ltebs-polimi/AY2122_II_Project-1/Project_LTEBS/Saturimetro.cydsn/I2C_Interface.c

/*
* This file includes all the required source code to interface
* the I2C peripheral.
*/


#include "I2C_Interface.h" 
#include "I2C_Master.h"

    uint8_t I2C_Peripheral_Start(void) 
    {
        // Start I2C peripheral
        I2C_Master_Start();  
        
        // Return no error since start function does not return any error
        return I2C_NO_ERROR;
    }
    
    
    uint8_t I2C_Peripheral_Stop(void)
    {
        // Stop I2C peripheral
        I2C_Master_Stop();
        // Return no error since stop function does not return any error
        return I2C_NO_ERROR;
    }
    
    uint8_t I2C_Peripheral_SendStop(void)
    {
        I2C_Master_MasterSendStop();
        return I2C_NO_ERROR;
    }
    
    uint8_t I2C_Peripheral_ReadRegister(uint8_t device_address, 
                                            uint8_t register_address,
                                            uint8_t* data)
    {
        // Send start condition
        uint8_t error = I2C_Master_MasterSendStart(device_address,I2C_Master_WRITE_XFER_MODE);
        if (error == I2C_Master_MSTR_NO_ERROR)
        {
            // Write address of register to be read
            error = I2C_Master_MasterWriteByte(register_address);
            if (error == I2C_Master_MSTR_NO_ERROR)
            {
                // Send restart condition
                error = I2C_Master_MasterSendRestart(device_address, I2C_Master_READ_XFER_MODE);
                if (error == I2C_Master_MSTR_NO_ERROR)
                {
                    // Read data without acknowledgement
                    *data = I2C_Master_MasterReadByte(I2C_Master_ACK_DATA);
                    // Send stop condition and return no error
                    I2C_Master_MasterSendStop();
                    return I2C_NO_ERROR;
                }
            }
        }
        // Send stop condition if something went wrong
        I2C_Master_MasterSendStop();
        // Return error code
        return I2C_DEV_NOT_FOUND;
    }
    
    uint8_t I2C_Peripheral_ReadRegisterMulti(uint8_t device_address,
                                                uint8_t register_address,
                                                uint16_t register_count,
                                                uint8_t* data)
    {
        // Send start condition
        uint8_t error = I2C_Master_MasterSendStart(device_address,I2C_Master_WRITE_XFER_MODE);
        if (error == I2C_Master_MSTR_NO_ERROR)
        {
            // Write address of register to be read with the MSB equal to 1
            // register_address |= 0x80;
            error = I2C_Master_MasterWriteByte(register_address);
            if (error == I2C_Master_MSTR_NO_ERROR)
            {
                // Send restart condition
                error = I2C_Master_MasterSendRestart(device_address, I2C_Master_READ_XFER_MODE);
                if (error == I2C_Master_MSTR_NO_ERROR)
                {
                    // Continue reading until we have register to read
                    uint16_t counter = register_count;
                    while(counter>1)
                    {
                        data[register_count-counter] =
                            I2C_Master_MasterReadByte(I2C_Master_ACK_DATA);
                        counter--;
                    }
                    // Read last data without acknowledgement
                    data[register_count-1]
                        = I2C_Master_MasterReadByte(I2C_Master_NAK_DATA);
                    // Send stop condition and return no error
                    I2C_Master_MasterSendStop();
                    return I2C_NO_ERROR;
                }
            }
        }
        // Send stop condition if something went wrong
        I2C_Master_MasterSendStop();
        // Return error code
        return I2C_DEV_NOT_FOUND;
    }
    
    uint8_t I2C_Peripheral_ReadRegisterMultiNoAddress(uint8_t device_address,
                                                      uint16_t register_count, 
                                                      uint8_t* data)
    {
        // Send restart condition
        uint8_t error = I2C_Master_MasterSendStart(device_address, I2C_Master_READ_XFER_MODE);
        if (error == I2C_Master_MSTR_NO_ERROR)
        {
            // Continue reading until we have register to read
            uint16_t counter = register_count;
            while(counter>1)
            {
                data[register_count-counter] =
                    I2C_Master_MasterReadByte(I2C_Master_ACK_DATA);
                counter--;
            }
            // Read last data without acknowledgement
            data[register_count-1] = I2C_Master_MasterReadByte(I2C_Master_NAK_DATA);
            // Send stop condition and return no error
            I2C_Master_MasterSendStop();
            return I2C_NO_ERROR;
        }
        // Send stop condition if something went wrong
        I2C_Master_MasterSendStop();
        // Return error code
        return I2C_DEV_NOT_FOUND;
    }
    
    uint8_t I2C_Peripheral_StartReadNoAddress(uint8_t device_address)
    {
        // Send restart condition
        uint8_t error = I2C_Master_MasterSendStart(device_address, I2C_Master_READ_XFER_MODE);
        if (error == I2C_Master_MSTR_NO_ERROR)
        {
            return I2C_NO_ERROR;
        }
        // Return error code
        return I2C_DEV_NOT_FOUND;
    }
    
    uint8_t I2C_Peripheral_ReadBytes(uint8_t* data, uint8_t len)
    {
        // Continue reading until we have register to read
        uint16_t counter = len;
        while(counter>1)
        {
            data[len-counter] = I2C_Master_MasterReadByte(I2C_Master_ACK_DATA);
            counter--;
        }
        
        return I2C_NO_ERROR;
    }
    
    uint8_t I2C_Peripheral_WriteRegister(uint8_t device_address,
                                            uint8_t register_address,
                                            uint8_t data)
    {
        // Send start condition
        uint8_t error = I2C_Master_MasterSendStart(device_address, I2C_Master_WRITE_XFER_MODE);
        if (error == I2C_Master_MSTR_NO_ERROR)
        {
            // Write register address
            error = I2C_Master_MasterWriteByte(register_address);
            if (error == I2C_Master_MSTR_NO_ERROR)
            {
                // Write byte of interest
                error = I2C_Master_MasterWriteByte(data);
                if (error == I2C_Master_MSTR_NO_ERROR)
                {
                    // Send stop condition
                    I2C_Master_MasterSendStop();
                    // Return with no error
                    return I2C_NO_ERROR;
                }
            }
        }
        // Send stop condition in case something didn't work out correctly
        I2C_Master_MasterSendStop();
        // Return error code
        return I2C_DEV_NOT_FOUND;
    }
    
    uint8_t I2C_Peripheral_WriteRegisterNoData(uint8_t device_address,
                                            uint8_t register_address)
    {
        // Send start condition
        uint8_t error = I2C_Master_MasterSendStart(device_address, I2C_Master_WRITE_XFER_MODE);
        if (error == I2C_Master_MSTR_NO_ERROR)
        {
            // Write register address
            error = I2C_Master_MasterWriteByte(register_address);
            if (error == I2C_Master_MSTR_NO_ERROR)
            {
                // Send stop condition
                I2C_Master_MasterSendStop();
                // Return with no error
                return I2C_NO_ERROR;
                
            }
        }
        // Send stop condition in case something didn't work out correctly
        I2C_Master_MasterSendStop();
        // Return error code
        return I2C_DEV_NOT_FOUND;
    }
    
    uint8_t I2C_Peripheral_WriteRegisterMulti(uint8_t device_address,
                                            uint8_t register_address,
                                            uint8_t register_count,
                                            uint8_t* data)
    {
        // Send start condition
        uint8_t error = I2C_Master_MasterSendStart(device_address, I2C_Master_WRITE_XFER_MODE);
        if (error == I2C_Master_MSTR_NO_ERROR)
        {
            // Write register address
            error = I2C_Master_MasterWriteByte(register_address);
            if (error == I2C_Master_MSTR_NO_ERROR)
            {
                // Continue writing until we have data to write
                uint8_t counter = register_count;
                while(counter > 0)
                {
                    error = I2C_Master_MasterWriteByte(data[register_count-counter]);
                    if (error != I2C_Master_MSTR_NO_ERROR)
                    {
                        // Send stop condition
                        I2C_Master_MasterSendStop();
                        // Return error code
                        return I2C_ERROR;
                    }
                    counter--;
                }
                // Send stop condition and return no error
                I2C_Master_MasterSendStop();
                return I2C_NO_ERROR;
            }
        }
        // Send stop condition in case something didn't work out correctly
        I2C_Master_MasterSendStop();
        // Return error code
        return I2C_DEV_NOT_FOUND;
    }
    
    
    uint8_t I2C_Peripheral_IsDeviceConnected(uint8_t device_address)
    {
        // Send a start condition followed by a stop condition
        uint8_t error = I2C_Master_MasterSendStart(device_address, I2C_Master_WRITE_XFER_MODE);
        I2C_Master_MasterSendStop();
        // If no error generated during stop, device is connected
        if (error == I2C_Master_MSTR_NO_ERROR)
        {
            return I2C_NO_ERROR;
        }
        else
        {
            return I2C_DEV_NOT_FOUND;
        }
        
    }

/* [] END OF FILE */
