ltebs-polimi/AY2122_II_Project-1/Project_LTEBS/Saturimetro.cydsn/algorithm.h

/* ========================================
 *
 * Copyright YOUR COMPANY, THE YEAR
 * All Rights Reserved
 * UNPUBLISHED, LICENSED SOFTWARE.
 *
 * CONFIDENTIAL AND PROPRIETARY INFORMATION
 * WHICH IS THE PROPERTY OF your company.
 *
 * ========================================
*/
/** \file algorithm.h ******************************************************
*
* Project: MAXREFDES117#
* Filename: algorithm.h
* Description: This module is the heart rate/SpO2 calculation algorithm header file
*
* Revision History:
*\n 1-18-2016 Rev 01.00 SK Initial release.
*\n
*
* --------------------------------------------------------------------
*
* This code follows the following naming conventions:
*
*\n char              ch_pmod_value
*\n char (array)      s_pmod_s_string[16]
*\n float             f_pmod_value
*\n int32_t           n_pmod_value
*\n int32_t (array)   an_pmod_value[16]
*\n int16_t           w_pmod_value
*\n int16_t (array)   aw_pmod_value[16]
*\n uint16_t          uw_pmod_value
*\n uint16_t (array)  auw_pmod_value[16]
*\n uint8_t           uch_pmod_value
*\n uint8_t (array)   auch_pmod_buffer[16]
*\n uint32_t          un_pmod_value
*\n int32_t *         pn_pmod_value
*
* ------------------------------------------------------------------------- */
/*******************************************************************************
* Copyright (C) 2015 Maxim Integrated Products, Inc., All Rights Reserved.
*
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
* Except as contained in this notice, the name of Maxim Integrated
* Products, Inc. shall not be used except as stated in the Maxim Integrated
* Products, Inc. Branding Policy.
*
* The mere transfer of this software does not imply any licenses
* of trade secrets, proprietary technology, copyrights, patents,
* trademarks, maskwork rights, or any other form of intellectual
* property whatsoever. Maxim Integrated Products, Inc. retains all
* ownership rights.
*******************************************************************************
*/
#ifndef ALGORITHM_H_
#define ALGORITHM_H_
#include "project.h"
//#include "mbed.h"

#define true 1
#define false 0
#define FS 50
#define BUFFER_SIZE  (FS*5) 
#define HR_FIFO_SIZE 7
#define MA4_SIZE  4 // DO NOT CHANGE
#define HAMMING_SIZE  5// DO NOT CHANGE
#define min(x,y) ((x) < (y) ? (x) : (y))

extern const uint16_t auw_hamm[31]; //Hamm=  long16(512* hamming(5)');
//uch_spo2_table is computed as  -45.060*ratioAverage* ratioAverage + 30.354 *ratioAverage + 94.845 ;
extern const uint8_t uch_spo2_table[184];



void maxim_heart_rate_and_oxygen_saturation(uint32_t *pun_ir_buffer ,  int32_t n_ir_buffer_length, uint32_t *pun_red_buffer ,   int32_t *pn_spo2, int8_t *pch_spo2_valid ,  int32_t *pn_heart_rate , int8_t  *pch_hr_valid);
void maxim_find_peaks( int32_t *pn_locs, int32_t *pn_npks,  int32_t *pn_x, int32_t n_size, int32_t n_min_height, int32_t n_min_distance, int32_t n_max_num );
void maxim_peaks_above_min_height( int32_t *pn_locs, int32_t *pn_npks,  int32_t *pn_x, int32_t n_size, int32_t n_min_height );
void maxim_remove_close_peaks( int32_t *pn_locs, int32_t *pn_npks,   int32_t  *pn_x, int32_t n_min_distance );
void maxim_sort_ascend( int32_t *pn_x, int32_t n_size );
void maxim_sort_indices_descend(  int32_t  *pn_x, int32_t *pn_indx, int32_t n_size);

#endif /* ALGORITHM_H_ */
/* [] END OF FILE */
