ltebs-polimi/AY2122_II_Project-1/Project_LTEBS/Saturimetro.cydsn/SpO2_HR.h

/* ========================================
 *
 * Copyright YOUR COMPANY, THE YEAR
 * All Rights Reserved
 * UNPUBLISHED, LICENSED SOFTWARE.
 *
 * CONFIDENTIAL AND PROPRIETARY INFORMATION
 * WHICH IS THE PROPERTY OF your company.
 *
 * ========================================
*/

#include "project.h"
#include <stdbool.h>

#define FreqS 50                   //sampling frequency (nel codice Arduino era 25)
#define BUFFER_SIZE (FreqS * 4)     // così da avere una Buffer Size di 200 
#define MA4_SIZE 4                // DONOT CHANGE
#define min(x,y) ((x) < (y) ? (x) : (y)) //Defined in Arduino.h */

//uch_spo2_table is approximated as  -45.060*ratioAverage* ratioAverage + 30.354 *ratioAverage + 94.845 ;
/*const uint8_t uch_spo2_table[100]={100, 99, 98, 97, 96, 95, 94, 93, 92, 91, 90, 89, 88, 87, 86, 85, 84, 83, 82, 
                                    81, 80, 79, 78, 77, 76, 75, 74, 73, 72, 71, 70, 69, 68, 
                                    67, 66, 65, 64, 63, 62, 61, 60, 59, 58, 57, 56, 55, 54, 53, 52, 51, 
                                    50, 49, 48, 47, 46, 45, 44, 43, 42, 41, 40, 39, 38, 37, 36, 35, 34, 33, 32, 
                                    31, 30, 29, 28, 27, 26, 25, 24, 23, 22, 21, 20, 19, 18, 17, 16, 15, 14, 13, 
                                    12, 11, 10, 9, 8, 7, 6, 5, 4, 3, 2, 1 } ;*/
int32_t an_x[BUFFER_SIZE]; //ir
int32_t an_y[BUFFER_SIZE]; //red

void maxim_heart_rate_and_oxygen_saturation(uint32_t *pun_ir_buffer, int32_t n_buffer_length, uint32_t *pun_red_buffer, int32_t *pn_spo2, int8_t *pch_spo2_valid, int32_t *pn_heart_rate, int8_t *pch_hr_valid);

void maxim_find_peaks(int32_t *pn_locs, int32_t *n_npks,  int32_t  *pn_x, int32_t n_size, int32_t n_min_height, int32_t n_min_distance, int32_t n_max_num);
void maxim_peaks_above_min_height(int32_t *pn_locs, int32_t *n_npks,  int32_t  *pn_x, int32_t n_size, int32_t n_min_height);
void maxim_remove_close_peaks(int32_t *pn_locs, int32_t *pn_npks, int32_t *pn_x, int32_t n_min_distance);
void maxim_sort_ascend(int32_t  *pn_x, int32_t n_size);
void maxim_sort_indices_descend(int32_t  *pn_x, int32_t *pn_indx, int32_t n_size);


/* [] END OF FILE */
