ltebs-polimi/AY2122_II_Project-1/Project_LTEBS/Saturimetro.cydsn/codegentemp/Connection_LED_aliases.h

/*******************************************************************************
* File Name: Connection_LED.h  
* Version 2.20
*
* Description:
*  This file contains the Alias definitions for Per-Pin APIs in cypins.h. 
*  Information on using these APIs can be found in the System Reference Guide.
*
* Note:
*
********************************************************************************
* Copyright 2008-2015, Cypress Semiconductor Corporation.  All rights reserved.
* You may use this file only in accordance with the license, terms, conditions, 
* disclaimers, and limitations in the end user license agreement accompanying 
* the software package with which this file was provided.
*******************************************************************************/

#if !defined(CY_PINS_Connection_LED_ALIASES_H) /* Pins Connection_LED_ALIASES_H */
#define CY_PINS_Connection_LED_ALIASES_H

#include "cytypes.h"
#include "cyfitter.h"


/***************************************
*              Constants        
***************************************/
#define Connection_LED_0			(Connection_LED__0__PC)
#define Connection_LED_0_INTR	((uint16)((uint16)0x0001u << Connection_LED__0__SHIFT))

#define Connection_LED_INTR_ALL	 ((uint16)(Connection_LED_0_INTR))

#endif /* End Pins Connection_LED_ALIASES_H */


/* [] END OF FILE */
