ltebs-polimi/AY2122_II_Project-1/Project_LTEBS/Saturimetro.cydsn/codegentemp/isr_SM.h

/*******************************************************************************
* File Name: isr_SM.h
* Version 1.71
*
*  Description:
*   Provides the function definitions for the Interrupt Controller.
*
*
********************************************************************************
* Copyright 2008-2015, Cypress Semiconductor Corporation.  All rights reserved.
* You may use this file only in accordance with the license, terms, conditions, 
* disclaimers, and limitations in the end user license agreement accompanying 
* the software package with which this file was provided.
*******************************************************************************/
#if !defined(CY_ISR_isr_SM_H)
#define CY_ISR_isr_SM_H


#include <cytypes.h>
#include <cyfitter.h>

/* Interrupt Controller API. */
void isr_SM_Start(void);
void isr_SM_StartEx(cyisraddress address);
void isr_SM_Stop(void);

CY_ISR_PROTO(isr_SM_Interrupt);

void isr_SM_SetVector(cyisraddress address);
cyisraddress isr_SM_GetVector(void);

void isr_SM_SetPriority(uint8 priority);
uint8 isr_SM_GetPriority(void);

void isr_SM_Enable(void);
uint8 isr_SM_GetState(void);
void isr_SM_Disable(void);

void isr_SM_SetPending(void);
void isr_SM_ClearPending(void);


/* Interrupt Controller Constants */

/* Address of the INTC.VECT[x] register that contains the Address of the isr_SM ISR. */
#define isr_SM_INTC_VECTOR            ((reg32 *) isr_SM__INTC_VECT)

/* Address of the isr_SM ISR priority. */
#define isr_SM_INTC_PRIOR             ((reg8 *) isr_SM__INTC_PRIOR_REG)

/* Priority of the isr_SM interrupt. */
#define isr_SM_INTC_PRIOR_NUMBER      isr_SM__INTC_PRIOR_NUM

/* Address of the INTC.SET_EN[x] byte to bit enable isr_SM interrupt. */
#define isr_SM_INTC_SET_EN            ((reg32 *) isr_SM__INTC_SET_EN_REG)

/* Address of the INTC.CLR_EN[x] register to bit clear the isr_SM interrupt. */
#define isr_SM_INTC_CLR_EN            ((reg32 *) isr_SM__INTC_CLR_EN_REG)

/* Address of the INTC.SET_PD[x] register to set the isr_SM interrupt state to pending. */
#define isr_SM_INTC_SET_PD            ((reg32 *) isr_SM__INTC_SET_PD_REG)

/* Address of the INTC.CLR_PD[x] register to clear the isr_SM interrupt. */
#define isr_SM_INTC_CLR_PD            ((reg32 *) isr_SM__INTC_CLR_PD_REG)


#endif /* CY_ISR_isr_SM_H */


/* [] END OF FILE */
